vakeesank99/PIR_sensor_module_using_basic_components/research for pir/2022-05-07_13-43-39.png

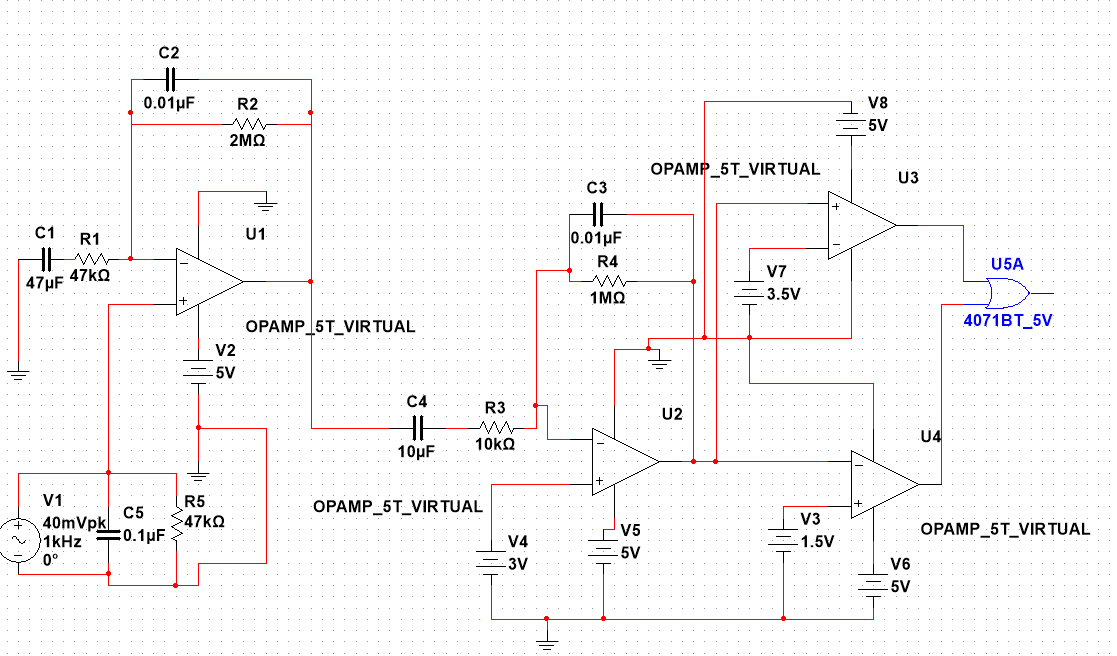
research for pir/2022-05-07_13-43-39.png
