vakeesank99/PIR_sensor_module_using_basic_components/research for pir/screenshot-from-2014-04-10-085805.webp

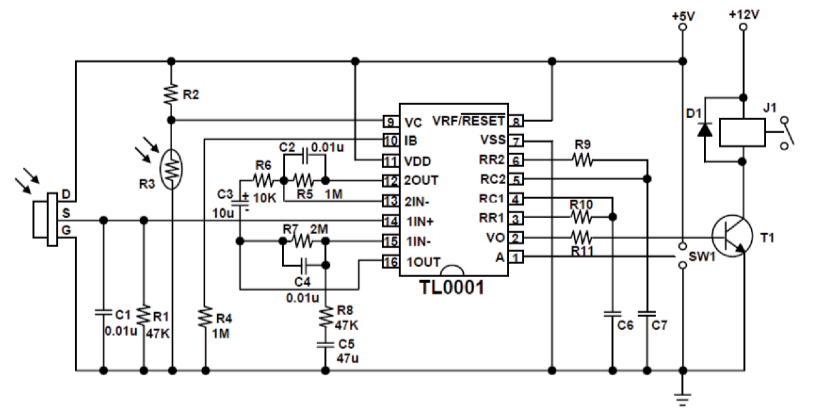
research for pir/screenshot-from-2014-04-10-085805.webp
