vakeesank99/PIR_sensor_module_using_basic_components/research for pir/STMicro2.jpg

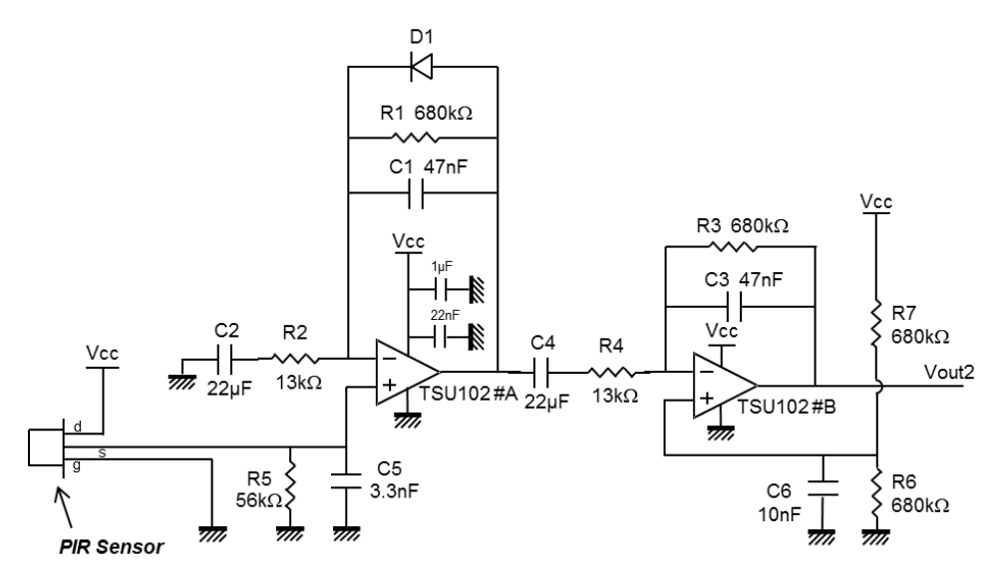
research for pir/STMicro2.jpg
