vakeesank99/PIR_sensor_module_using_basic_components/research for pir/Typical-amplifier-circuit-used-with-a-PIR-sensor-13.png

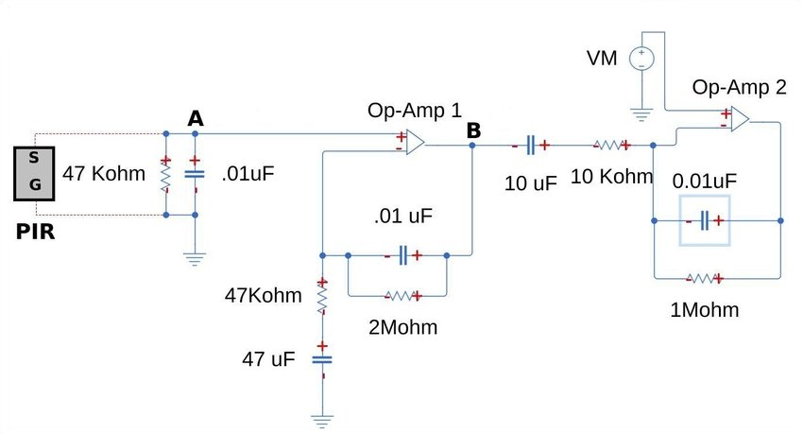
research for pir/Typical-amplifier-circuit-used-with-a-PIR-sensor-13.png
