vakeesank99/PIR_sensor_module_using_basic_components/Submitted documents/2.png

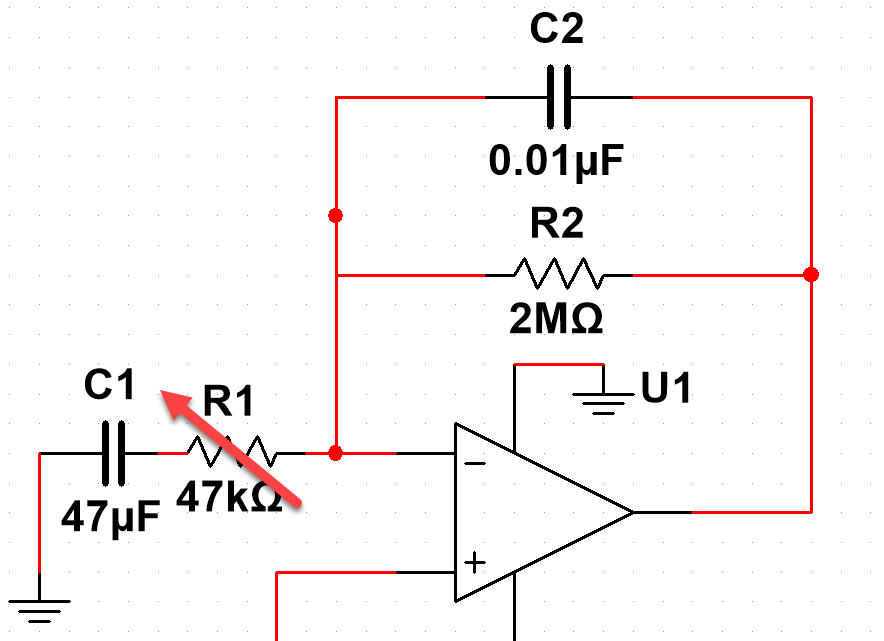
Submitted documents/2.png
